flesniak/mso5k-la-pod/img/pcb-complete-in-pcbnew.png

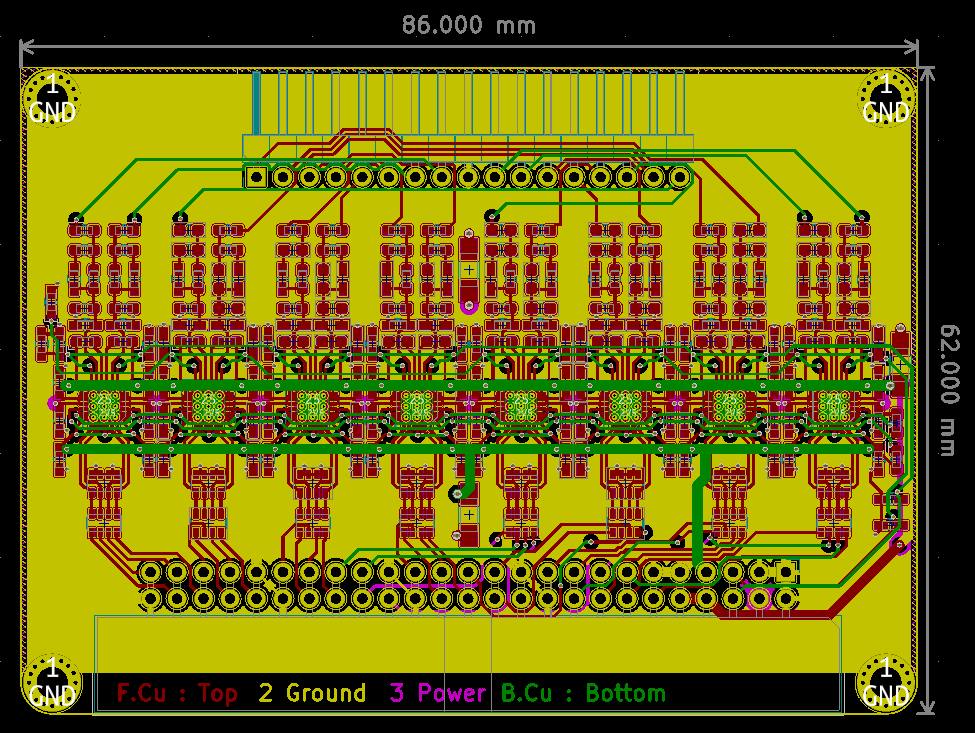
img/pcb-complete-in-pcbnew.png
