flesniak/mso5k-la-pod/panel-2019-03-20/panel-2019-03-20-3d.png

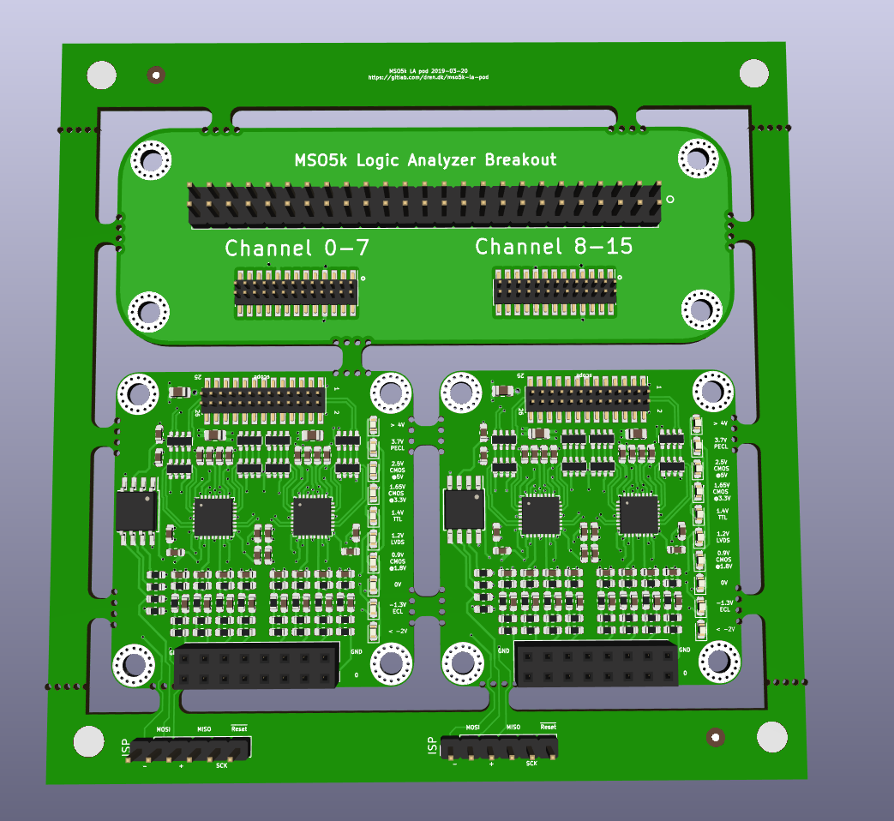
panel-2019-03-20/panel-2019-03-20-3d.png
