flesniak/mso5k-la-pod/img/e1-fix.png

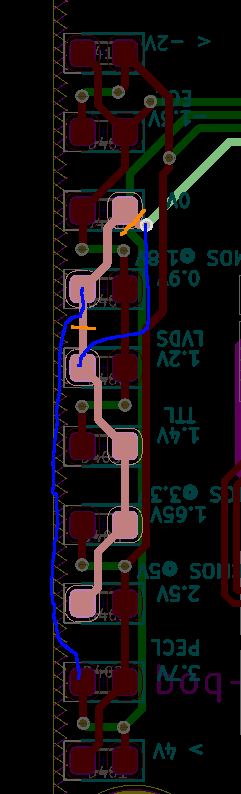
img/e1-fix.png
